svenpetersen1965/C64-Promenade-Model-D/Resources/C64_Promenade_ModelC1_bom.jpg

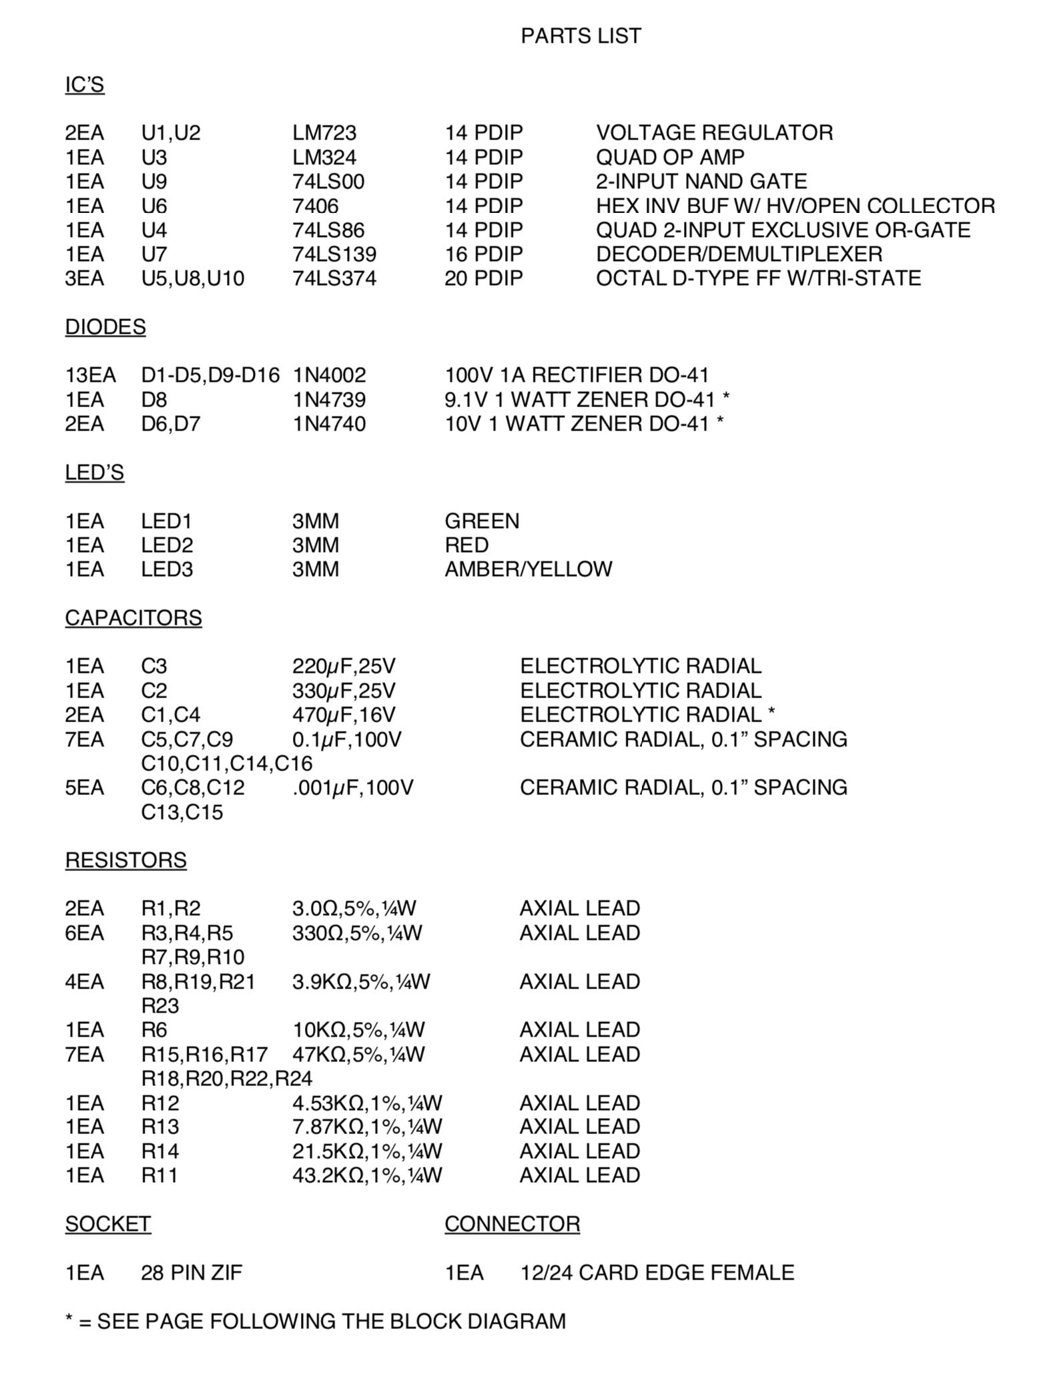
Resources/C64_Promenade_ModelC1_bom.jpg
